enheragu/hitos_setup/media/web_manager_phone_dark_complete.png

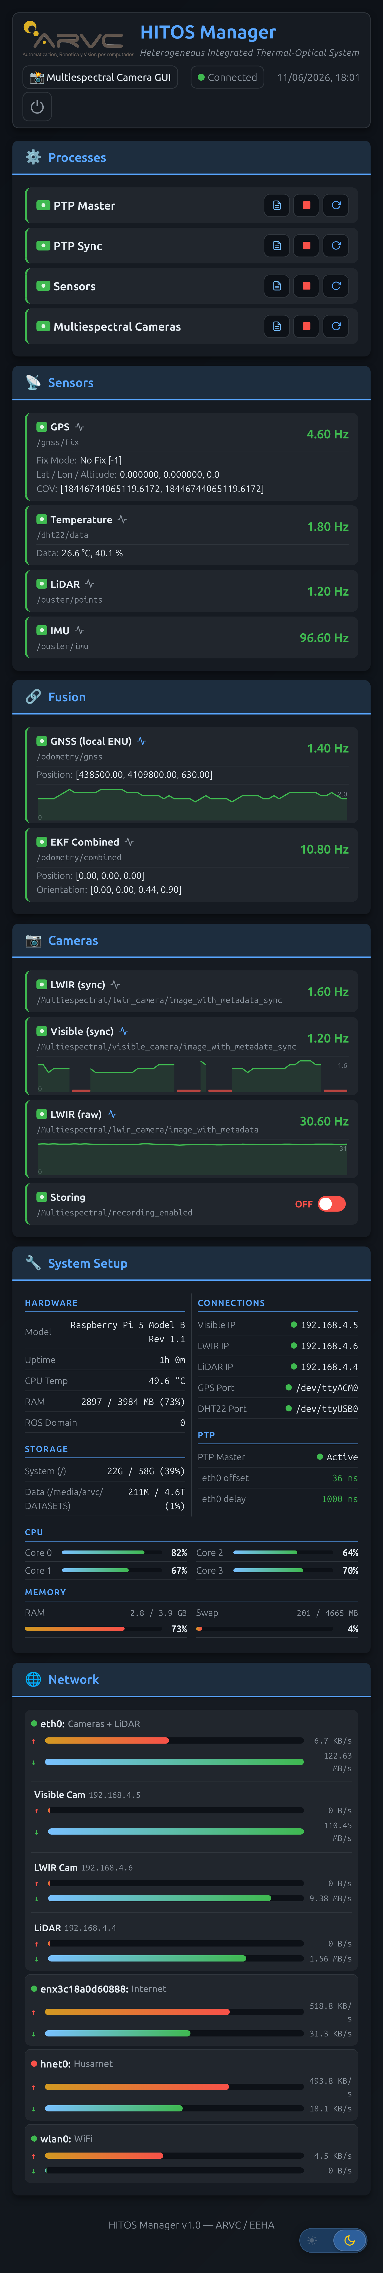
media/web_manager_phone_dark_complete.png
